AdamLaurie/chronos-rb/firmware/src/wifi_manager.c

/**
 * CHRONOS-Rb WiFi Manager Module
 * 
 * Manages WiFi connectivity for the Pico 2-W.
 * 
 * Copyright (c) 2025 - Open Source Hardware Project
 * License: MIT
 */

#include <stdio.h>
#include <string.h>
#include "pico/stdlib.h"
#include "pico/cyw43_arch.h"
#include "hardware/watchdog.h"
#include "lwip/netif.h"

#include "chronos_rb.h"
#include "config.h"

/*============================================================================
 * PRIVATE VARIABLES
 *============================================================================*/

static bool wifi_initialized = false;
static bool wifi_connected = false;
static char current_ssid[33] = {0};
static uint32_t ip_address = 0;

/* Connection state tracking */
static uint32_t connection_attempts = 0;
static uint32_t last_connection_time = 0;
static uint32_t disconnection_count = 0;

/*============================================================================
 * INITIALIZATION
 *============================================================================*/

/**
 * Initialize WiFi subsystem
 */
void wifi_init(void) {
    printf("[WIFI] Initializing CYW43 WiFi...\n");
    
    if (cyw43_arch_init_with_country(CYW43_COUNTRY_USA)) {
        printf("[WIFI] ERROR: Failed to initialize WiFi\n");
        return;
    }
    
    cyw43_arch_enable_sta_mode();
    
    wifi_initialized = true;
    printf("[WIFI] WiFi initialized successfully\n");
    
    /* Print MAC address */
    uint8_t mac[6];
    cyw43_wifi_get_mac(&cyw43_state, CYW43_ITF_STA, mac);
    printf("[WIFI] MAC: %02X:%02X:%02X:%02X:%02X:%02X\n",
           mac[0], mac[1], mac[2], mac[3], mac[4], mac[5]);
}

/*============================================================================
 * CONNECTION MANAGEMENT
 *============================================================================*/

/**
 * Connect to WiFi network (non-blocking with manual polling)
 */
bool wifi_connect(const char *ssid, const char *password) {
    if (!wifi_initialized) {
        printf("[WIFI] ERROR: WiFi not initialized\n");
        return false;
    }

    printf("[WIFI] Connecting to '%s'...\n", ssid);
    connection_attempts++;

    /* Start async connection */
    int result = cyw43_arch_wifi_connect_async(ssid, password, CYW43_AUTH_WPA2_AES_PSK);
    if (result != 0) {
        printf("[WIFI] ERROR: Failed to start connection (error %d)\n", result);
        wifi_connected = false;
        g_wifi_connected = false;
        return false;
    }

    /* Poll for IP address with timeout (30s in 100ms chunks) */
    for (int i = 0; i < 300; i++) {
        sleep_ms(100);
        watchdog_update();

        /* Check if we got an IP address (most reliable indicator) */
        struct netif *netif = netif_default;
        if (netif != NULL && !ip4_addr_isany_val(*netif_ip4_addr(netif))) {
            ip_address = ip4_addr_get_u32(netif_ip4_addr(netif));
            printf("[WIFI] Connected! IP: %lu.%lu.%lu.%lu\n",
                   ip_address & 0xFF,
                   (ip_address >> 8) & 0xFF,
                   (ip_address >> 16) & 0xFF,
                   (ip_address >> 24) & 0xFF);

            strncpy(current_ssid, ssid, sizeof(current_ssid) - 1);
            wifi_connected = true;
            g_wifi_connected = true;
            last_connection_time = time_us_32() / 1000000;
            return true;
        }

        /* Check for definite failure states */
        int status = cyw43_wifi_link_status(&cyw43_state, CYW43_ITF_STA);
        if (status == CYW43_LINK_FAIL || status == CYW43_LINK_BADAUTH) {
            printf("[WIFI] ERROR: Connection failed (status %d)\n", status);
            break;
        }

        /* Print progress every 5 seconds */
        if (i > 0 && i % 50 == 0) {
            if (status >= CYW43_LINK_JOIN) {
                printf("[WIFI] Associated, waiting for IP... (%d s)\n", i / 10);
            } else {
                printf("[WIFI] Connecting... (%d s)\n", i / 10);
            }
        }
    }

    /* Connection failed or timed out */
    cyw43_wifi_leave(&cyw43_state, CYW43_ITF_STA);
    wifi_connected = false;
    g_wifi_connected = false;
    printf("[WIFI] Connection timed out or failed\n");
    return false;
}

/**
 * Disconnect from WiFi
 */
void wifi_disconnect(void) {
    if (wifi_connected) {
        cyw43_wifi_leave(&cyw43_state, CYW43_ITF_STA);
        wifi_connected = false;
        g_wifi_connected = false;
        ip_address = 0;
        printf("[WIFI] Disconnected\n");
    }
}

/**
 * Check if WiFi is connected
 */
bool wifi_is_connected(void) {
    return wifi_connected && (cyw43_wifi_link_status(&cyw43_state, CYW43_ITF_STA) == CYW43_LINK_JOIN);
}

/**
 * Get current IP address
 */
uint32_t get_ip_address(void) {
    return ip_address;
}

/**
 * Get IP address as string
 */
void get_ip_address_str(char *buf, size_t len) {
    snprintf(buf, len, "%lu.%lu.%lu.%lu",
             ip_address & 0xFF,
             (ip_address >> 8) & 0xFF,
             (ip_address >> 16) & 0xFF,
             (ip_address >> 24) & 0xFF);
}

/*============================================================================
 * WIFI TASK
 *============================================================================*/

/* Track if network services have been started */
static bool network_services_started = false;

void wifi_mark_services_started(void) {
    network_services_started = true;
}

/**
 * WiFi maintenance task - call periodically
 * Handles connection monitoring and automatic reconnection
 */
void wifi_task(void) {
    static uint64_t last_check = 0;
    static uint64_t last_reconnect_attempt = 0;
    uint64_t now = time_us_64();

    /* Check connection status every second */
    if (now - last_check < 1000000) {
        return;
    }
    last_check = now;

    if (!wifi_initialized) {
        return;
    }

    /* Poll lwIP regardless of connection state */
    cyw43_arch_poll();

    /* Check link status */
    int link_status = cyw43_wifi_link_status(&cyw43_state, CYW43_ITF_STA);

    if (wifi_connected && link_status != CYW43_LINK_JOIN) {
        /* Lost connection - clean up driver state */
        printf("[WIFI] Connection lost (status %d)\n", link_status);
        cyw43_wifi_leave(&cyw43_state, CYW43_ITF_STA);
        wifi_connected = false;
        g_wifi_connected = false;
        ip_address = 0;
        disconnection_count++;
    }

    /* Periodic reconnection if not connected and auto-connect enabled */
    if (!wifi_connected && config_wifi_auto_connect_enabled()) {
        /* Try every 30 seconds */
        if (now - last_reconnect_attempt > 30000000ULL) {
            last_reconnect_attempt = now;
            config_t *cfg = config_get();
            printf("[WIFI] Attempting reconnection to '%s'...\n", cfg->wifi_ssid);

            if (wifi_connect(cfg->wifi_ssid, cfg->wifi_pass)) {
                printf("[WIFI] Reconnection successful!\n");

                /* Start network services if not already started */
                if (!network_services_started) {
                    extern void ntp_server_init(void);
                    extern void ptp_server_init(void);
                    extern void web_init(void);
                    ntp_server_init();
                    ptp_server_init();
                    web_init();
                    network_services_started = true;
                    printf("[WIFI] Network services started\n");
                }
            }
        }
    }
}

/**
 * Get WiFi signal strength (RSSI)
 */
int32_t wifi_get_rssi(void) {
    int32_t rssi;
    if (cyw43_wifi_get_rssi(&cyw43_state, &rssi) == 0) {
        return rssi;
    }
    return 0;
}

/**
 * Get WiFi statistics
 */
void wifi_get_statistics(uint32_t *attempts, uint32_t *disconnects) {
    *attempts = connection_attempts;
    *disconnects = disconnection_count;
}

/**
 * Scan for available networks
 */
void wifi_scan(void) {
    printf("[WIFI] Scanning for networks...\n");
    
    /* Note: Full scan implementation would require callback handling */
    /* This is a simplified version */
    
    cyw43_wifi_scan_options_t scan_options = {0};
    int result = cyw43_wifi_scan(&cyw43_state, &scan_options, NULL, NULL);
    
    if (result != 0) {
        printf("[WIFI] Scan failed: %d\n", result);
    }
}

/**
 * Get current SSID
 */
const char* wifi_get_ssid(void) {
    return current_ssid;
}

/**
 * Check if WiFi is initialized
 */
bool wifi_is_initialized(void) {
    return wifi_initialized;
}
